SylvestreSakti/Grande-Illusion/feet_motion-capture/pointage.png

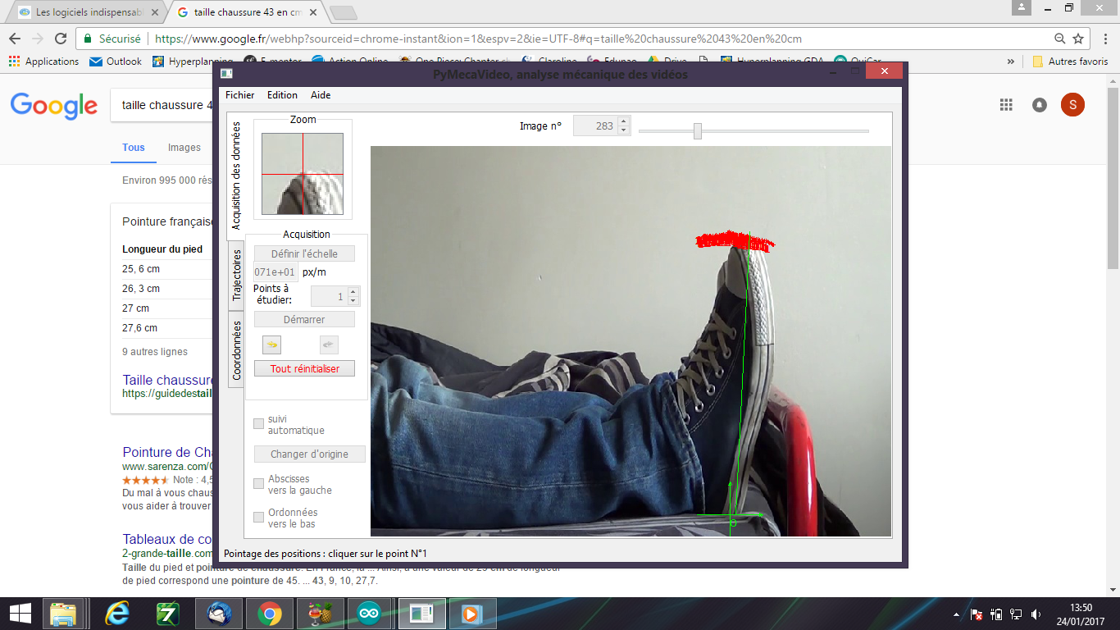
feet_motion-capture/pointage.png
