SylvestreSakti/Grande-Illusion/GI_modeling/photos/table_truquee_1.jpg

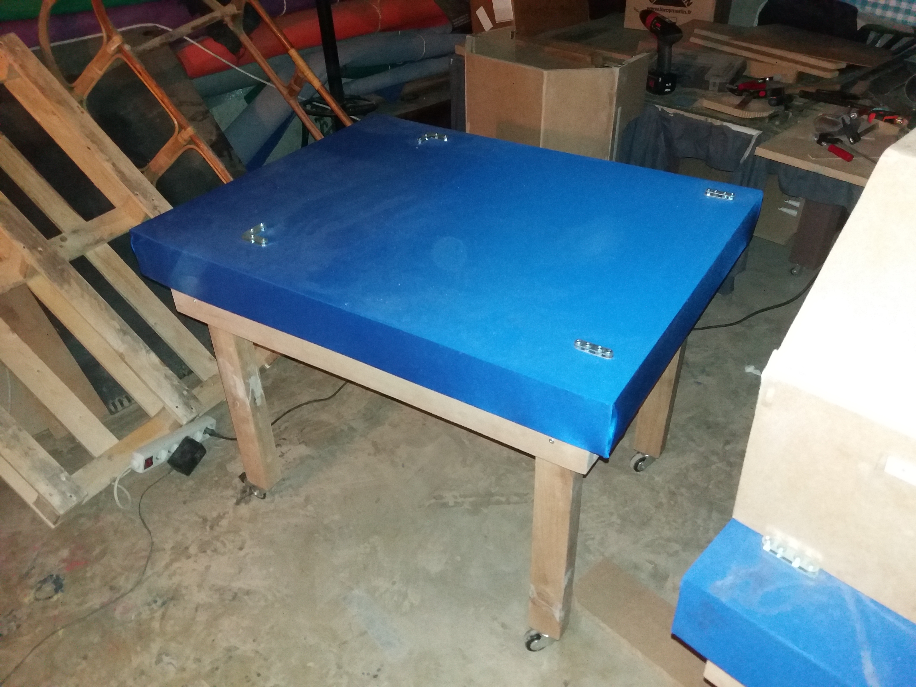
GI_modeling/photos/table_truquee_1.jpg
