SylvestreSakti/Grande-Illusion/GI_modeling/photos/table_truquee_2.jpg

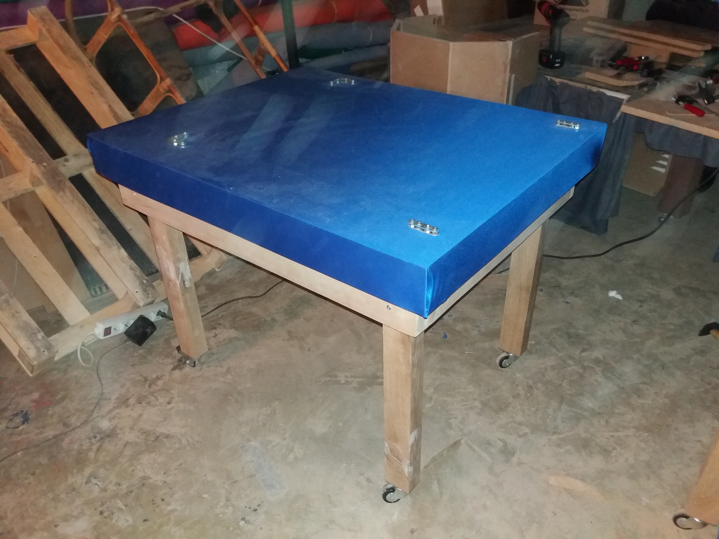
GI_modeling/photos/table_truquee_2.jpg
