SylvestreSakti/Grande-Illusion/GI_modeling/photos/tables_separees_2.jpg

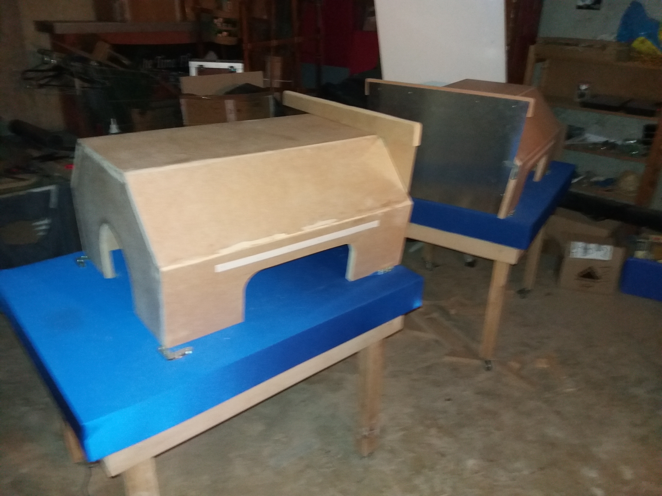
GI_modeling/photos/tables_separees_2.jpg
