SylvestreSakti/Grande-Illusion/GI_modeling/photos/verrouillage_volets_sortie.jpg

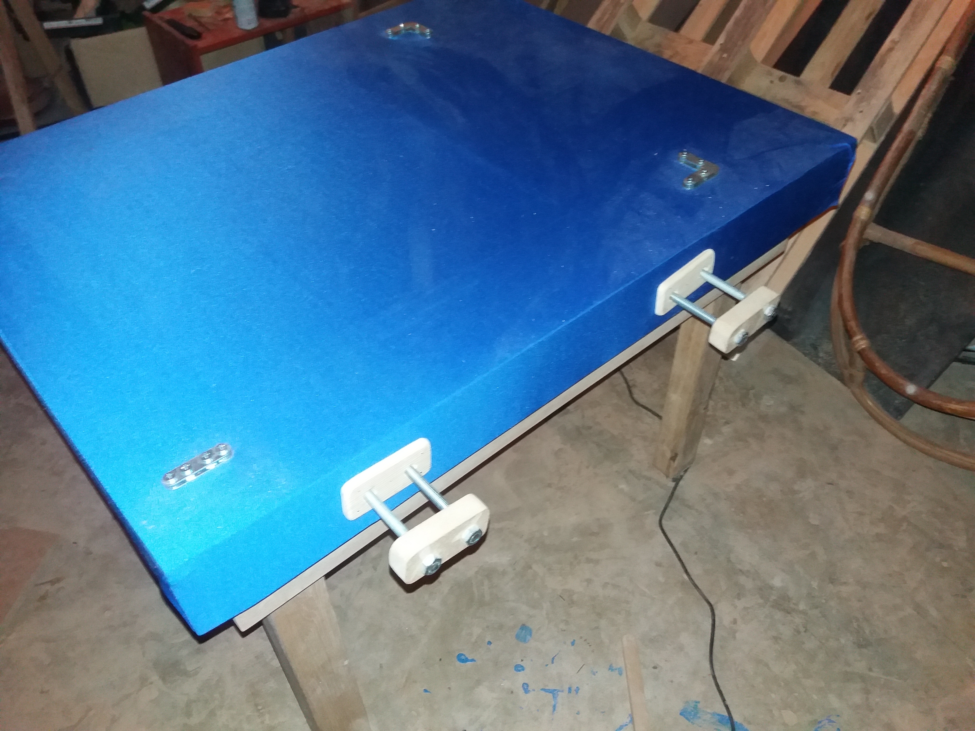
GI_modeling/photos/verrouillage_volets_sortie.jpg
