SylvestreSakti/Grande-Illusion/GI_modeling/photos/volets_rabattus_2.jpg

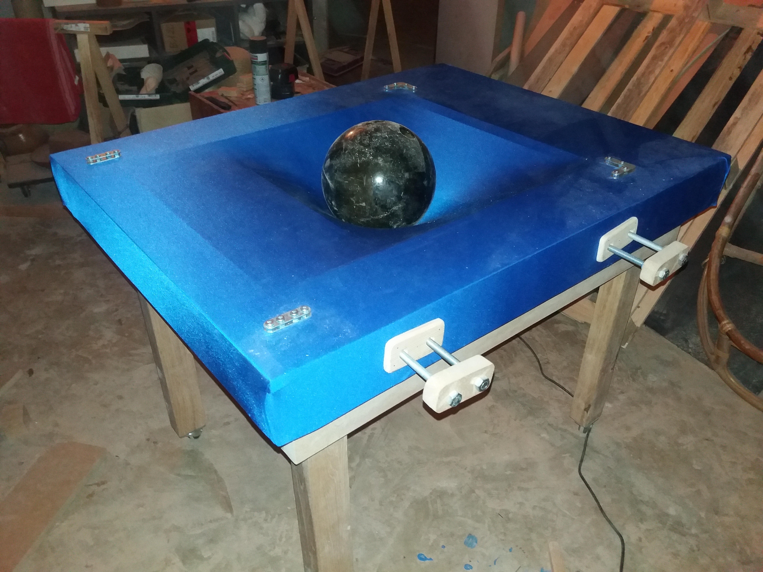
GI_modeling/photos/volets_rabattus_2.jpg
