SylvestreSakti/Grande-Illusion/GI_modeling/photos/vue_ensemble_pieds_1.jpg

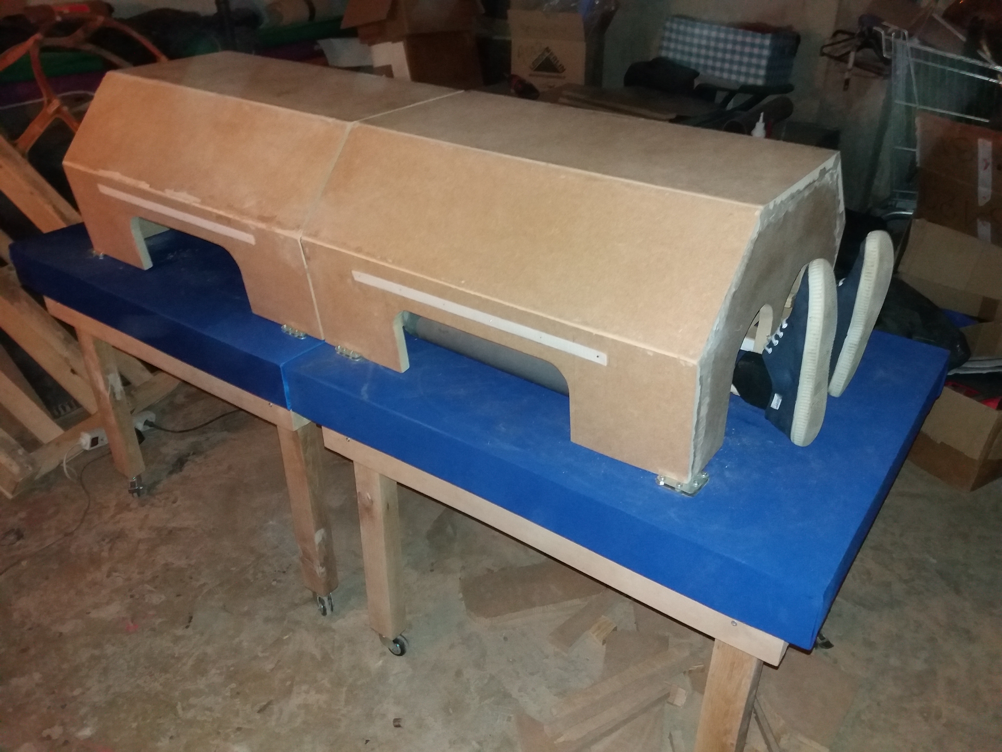
GI_modeling/photos/vue_ensemble_pieds_1.jpg
