SylvestreSakti/Grande-Illusion/GI_modeling/photos/vue_ensemble_tete.jpg

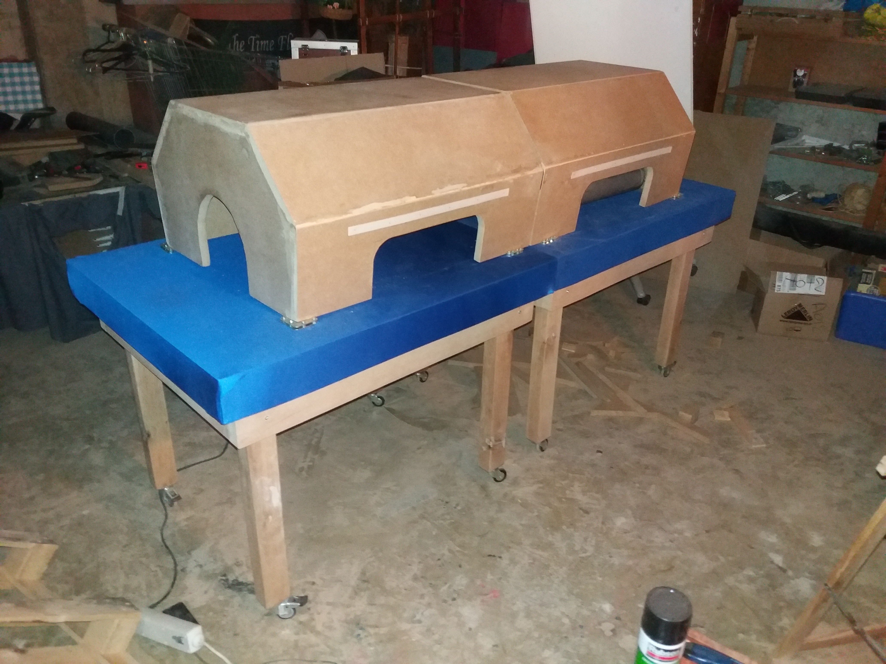
GI_modeling/photos/vue_ensemble_tete.jpg
