SylvestreSakti/Grande-Illusion/robotic_feet/boutons_modes_caisson.jpg

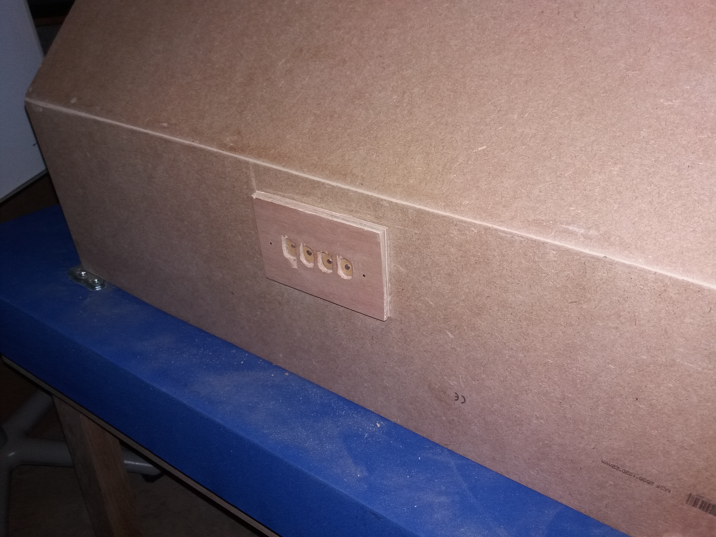
robotic_feet/boutons_modes_caisson.jpg
