SylvestreSakti/Grande-Illusion/robotic_feet/caisson_pieds_retourne.jpg

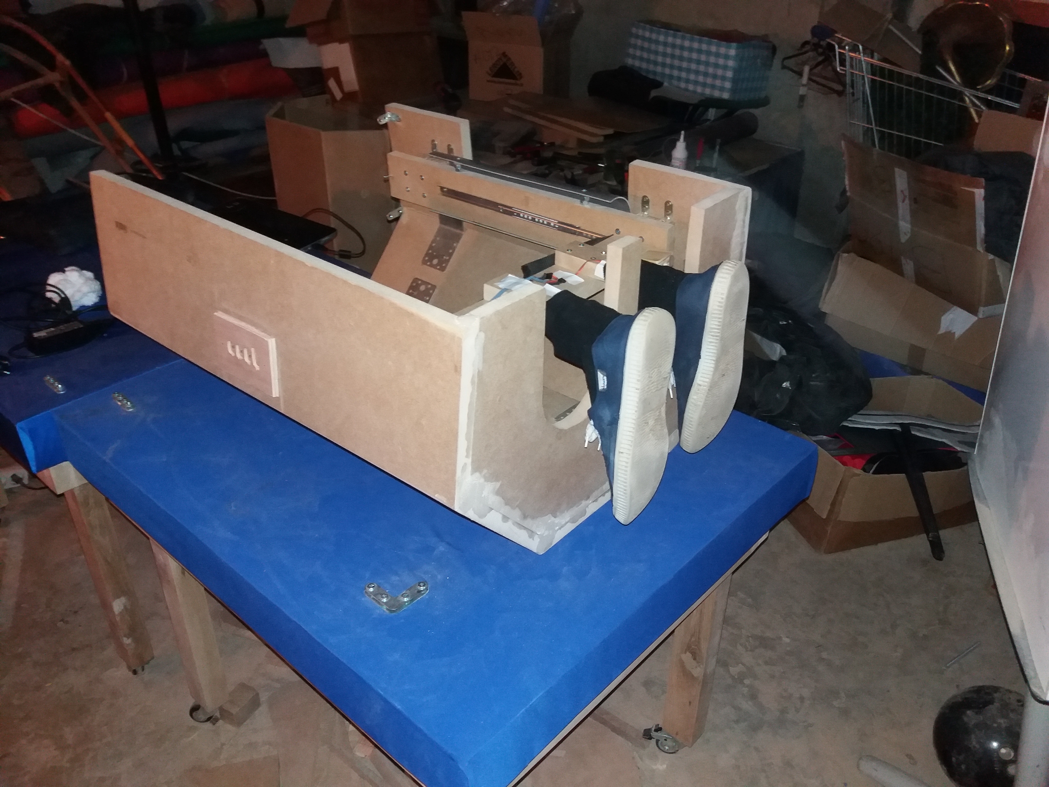
robotic_feet/caisson_pieds_retourne.jpg
