SylvestreSakti/Grande-Illusion/robotic_feet/circuit_electronique_1.jpg

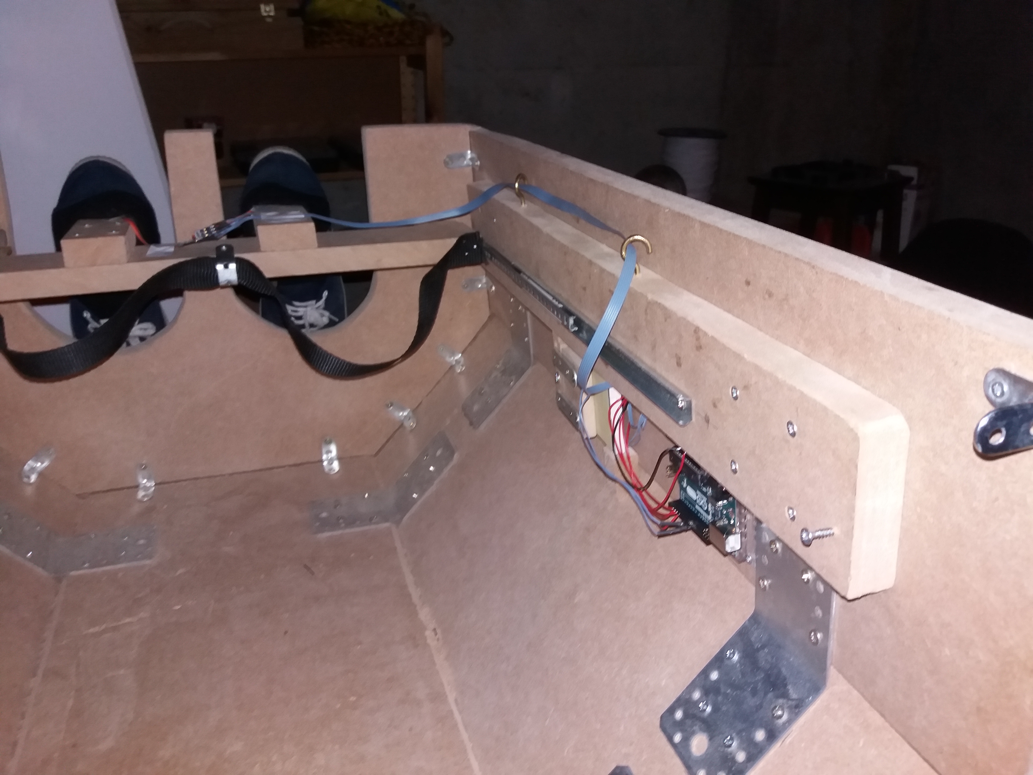
robotic_feet/circuit_electronique_1.jpg
