SylvestreSakti/Grande-Illusion/robotic_feet/fausse_jambe.jpg

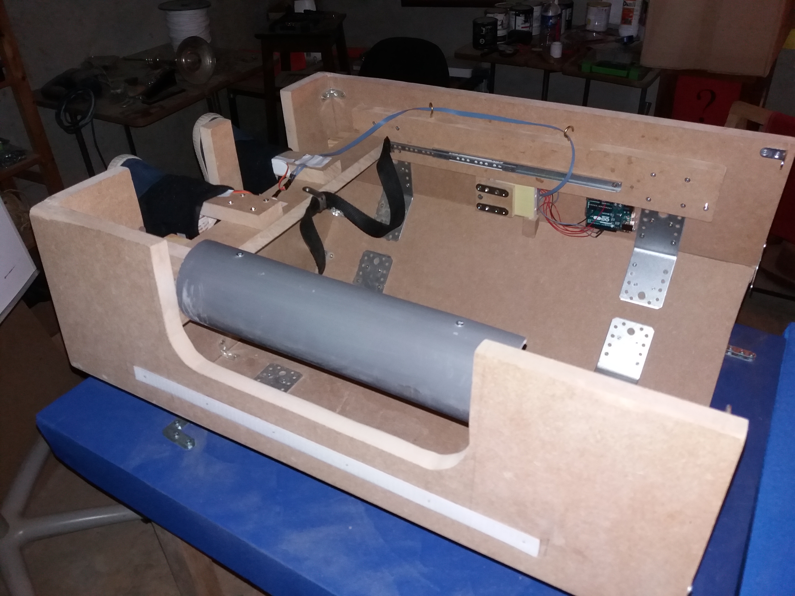
robotic_feet/fausse_jambe.jpg
