SylvestreSakti/Grande-Illusion/robotic_feet/glissiere_pieds_1.jpg

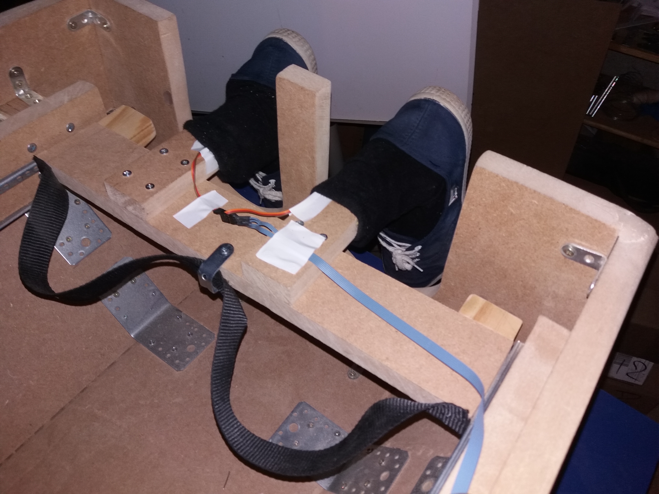
robotic_feet/glissiere_pieds_1.jpg
