SylvestreSakti/Grande-Illusion/robotic_feet/glissiere_pieds_2.jpg

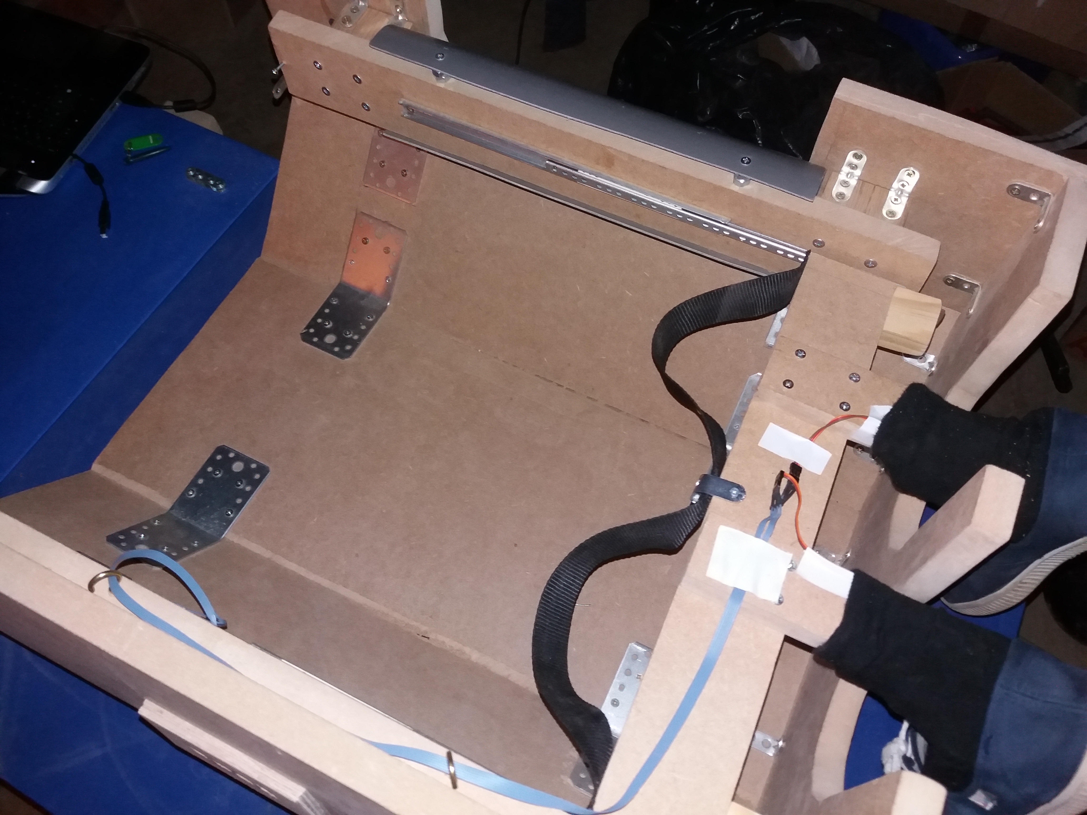
robotic_feet/glissiere_pieds_2.jpg
