SylvestreSakti/Grande-Illusion/electronic_board/plaque-test.JPG

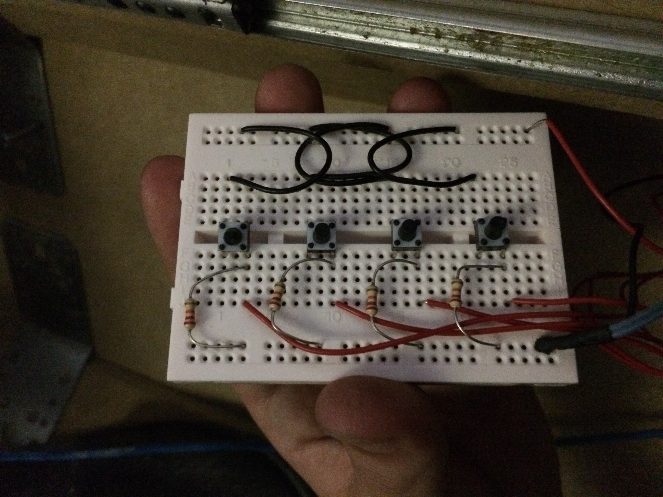
electronic_board/plaque-test.JPG
